cho0h5/keyboard61/firmware/tusb_config.h

#ifndef _TUSB_CONFIG_H_
#define _TUSB_CONFIG_H_

#ifndef BOARD_TUD_RHPORT
#define BOARD_TUD_RHPORT      0
#endif

#define CFG_TUD_ENABLED       1

#define CFG_TUD_HID               1

#define CFG_TUD_HID_EP_BUFSIZE    16

#endif /* _TUSB_CONFIG_H_ */
